ETS-Android4/Strobe/images/img-3.jpg

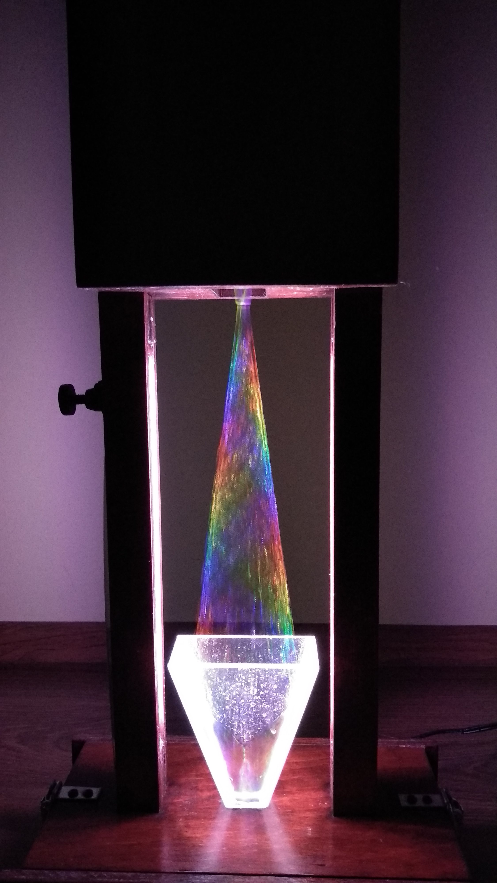
images/img-3.jpg
