ETS-Android4/Strobe/images/img_1.jpg

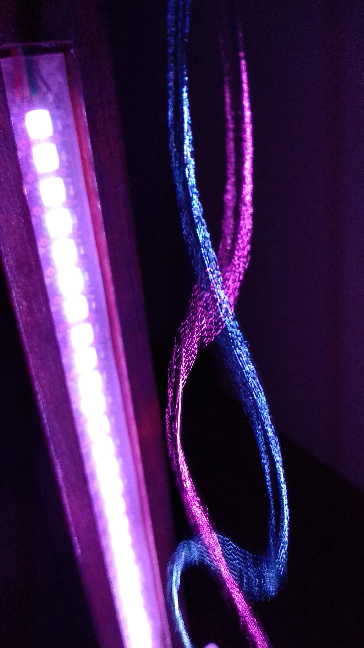
images/img_1.jpg
