ETS-Android4/Strobe/images/img_2.jpg

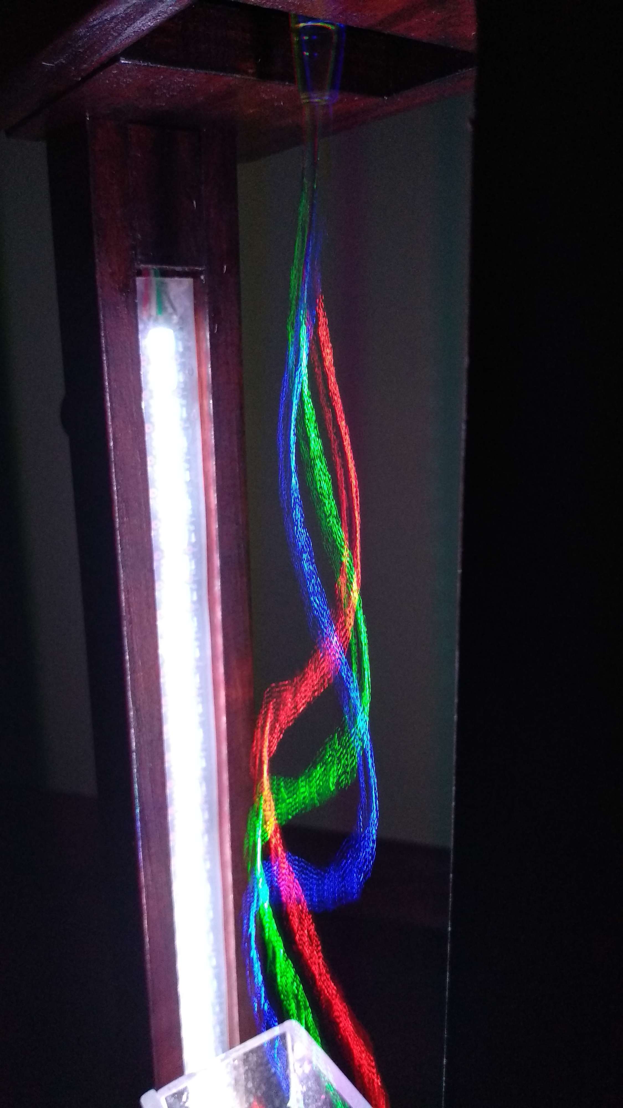
images/img_2.jpg
