ETS-Android4/Strobe/images/img_4.jpg

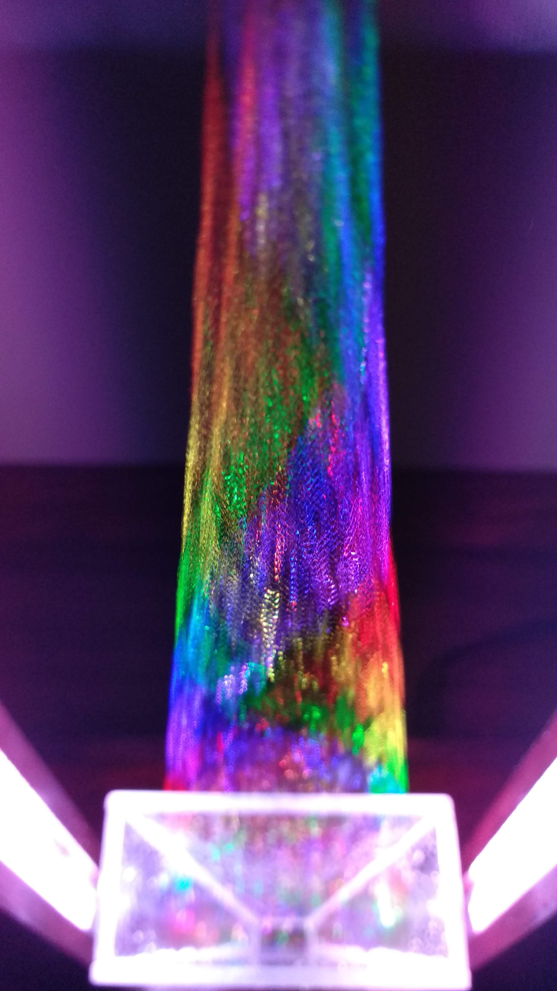
images/img_4.jpg
